mikalhart/Glowing-Puck-Network/Collateral/Case.scad

use <Case-modules.scad>
translate([0, 0, 40]) Top();
Bottom();
